coseyfannitutti/romeo/case/winkeyless/romeo-top-1-wkl.dxf

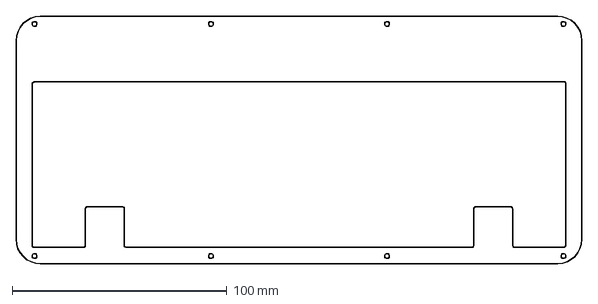
[picture p14: CAD file, 2020-03-20]
case/winkeyless/romeo-top-1-wkl.dxf
263.7 x 115.2 mm
